yuburoll/Boardloaf/images/boardloafAssembly0.jpg

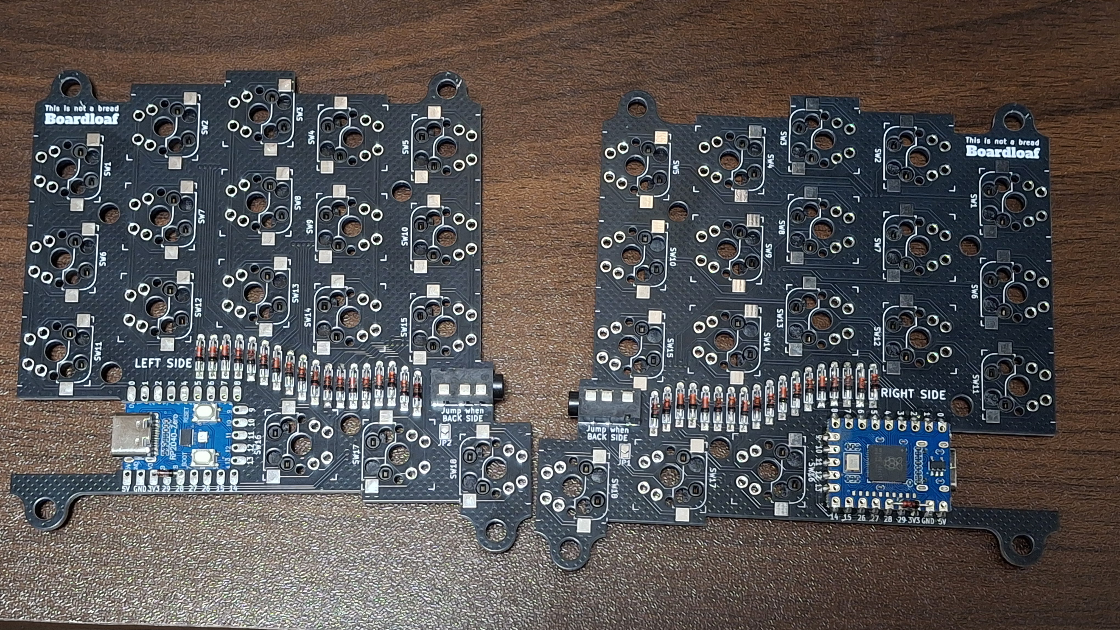
images/boardloafAssembly0.jpg
