yuburoll/Boardloaf/images/boardloafCaseAssembly0.jpg

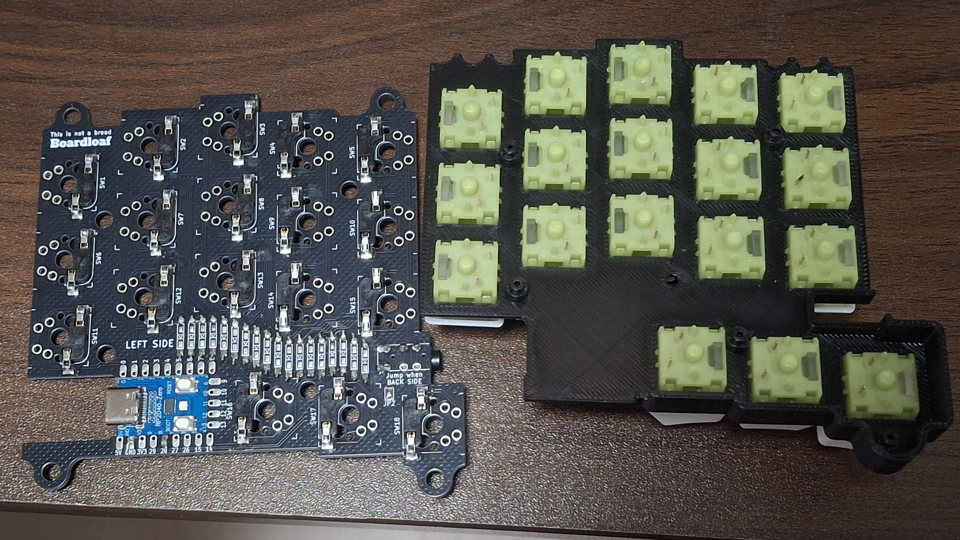
images/boardloafCaseAssembly0.jpg
