yuburoll/Boardloaf/images/boardloafCaseAssembly1.jpg

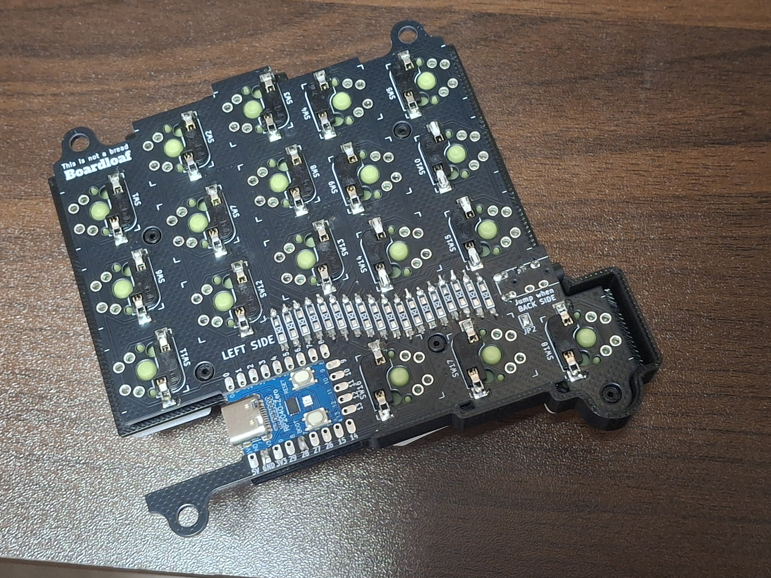
images/boardloafCaseAssembly1.jpg
