yuburoll/Boardloaf/images/boardloafCaseAssembly2.jpg

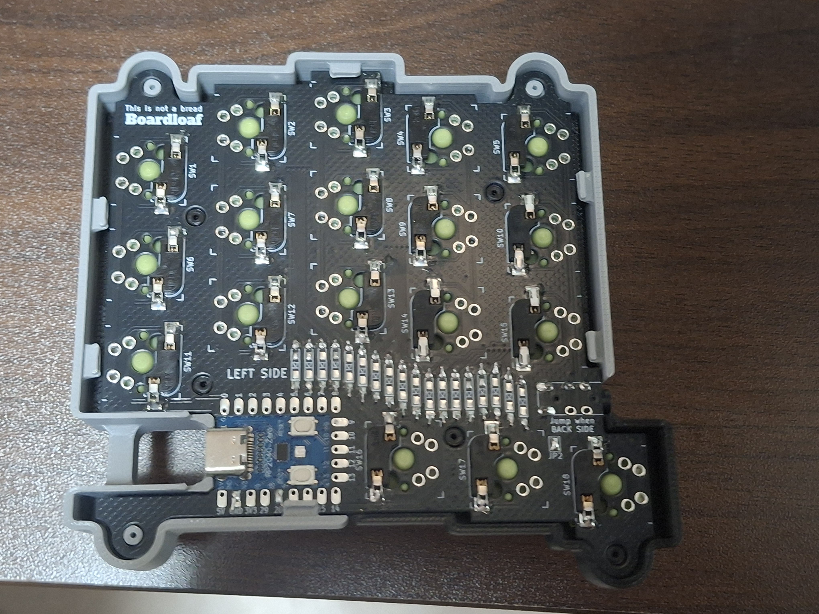
images/boardloafCaseAssembly2.jpg
