yuburoll/Boardloaf/images/boardloafDiodeSolder0.jpg

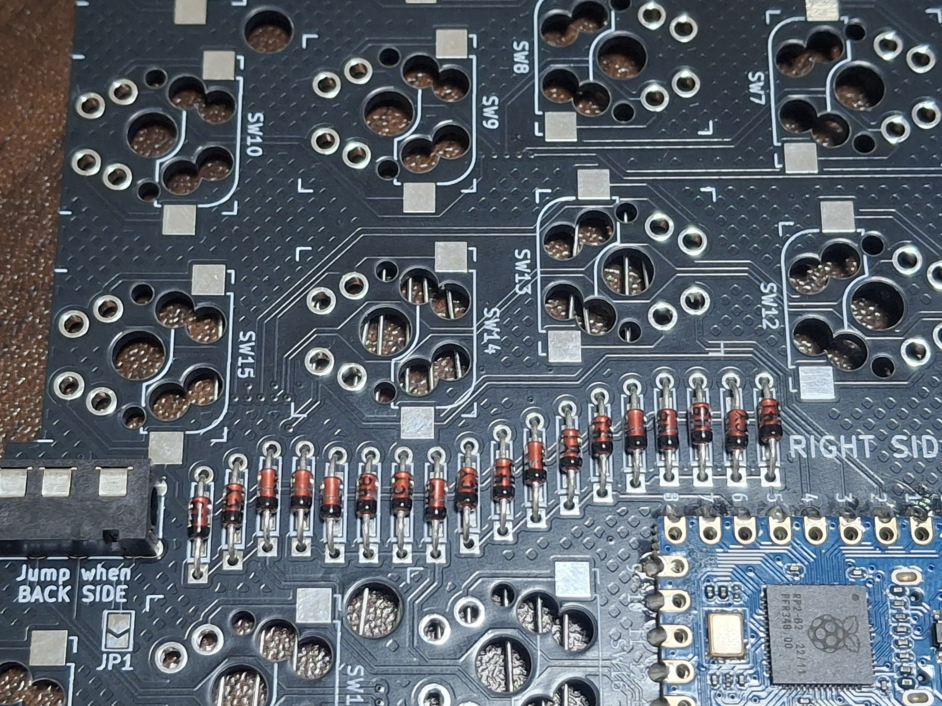
images/boardloafDiodeSolder0.jpg
