yuburoll/Boardloaf/images/boardloafDiodeSolder1.jpg

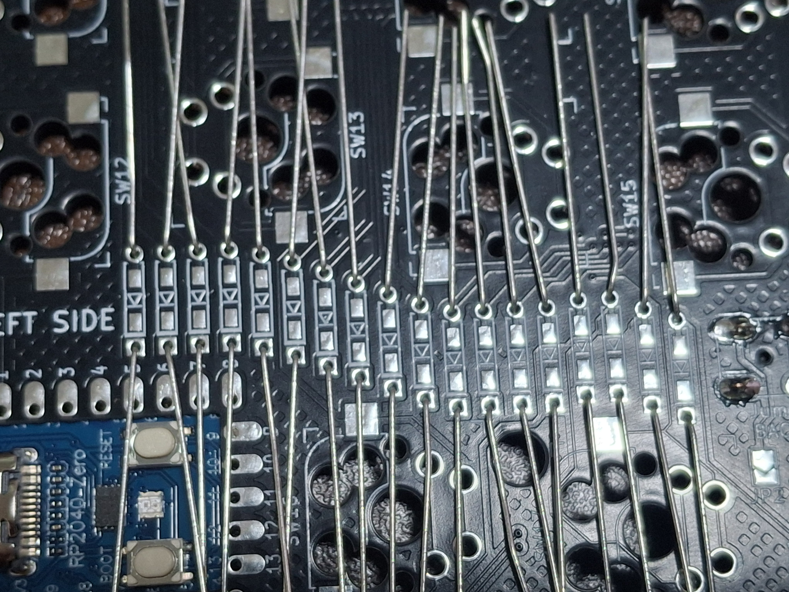
images/boardloafDiodeSolder1.jpg
